Dagi99/IM4_ProVelo/documentation/ressources/Veloklemme+Reed+halterung.stl.gif

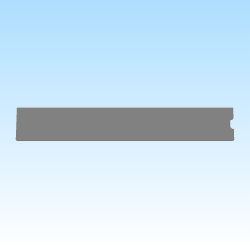
documentation/ressources/Veloklemme+Reed+halterung.stl.gif
