Dagi99/IM4_ProVelo/documentation/ressources/Veloklemme_1.stl.gif

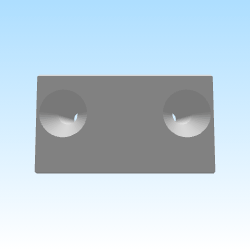
documentation/ressources/Veloklemme_1.stl.gif
